katzcreates/BMOctoprint/Print Files/BMOctoprint_DisplayMount02.stl

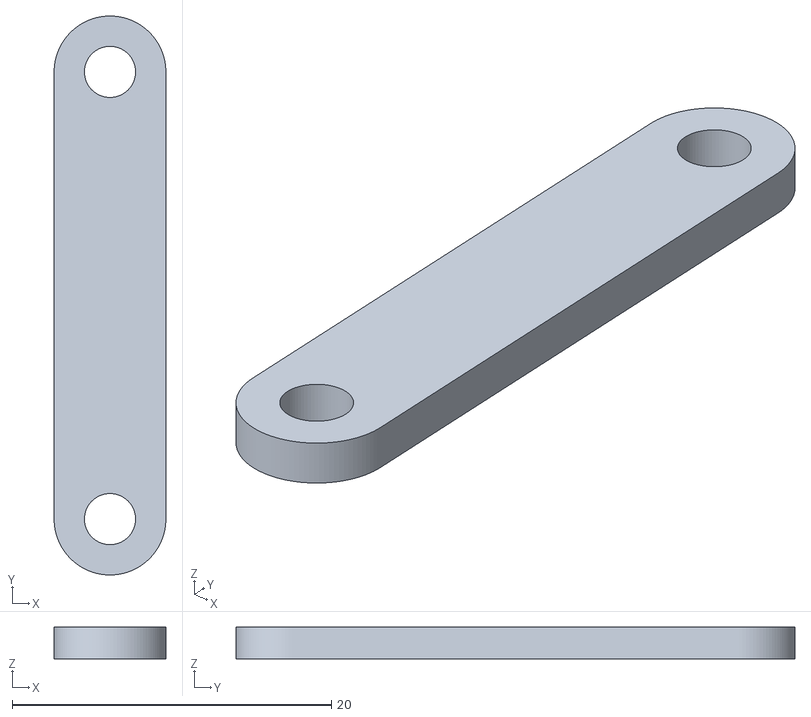
[picture p16: CAD file, 2022-08-17]
Print Files/BMOctoprint_DisplayMount02.stl
7.00 x 35.0 x 2.00
