katzcreates/BMOctoprint/Print Files/BMOctoprint_LegPlug.stl

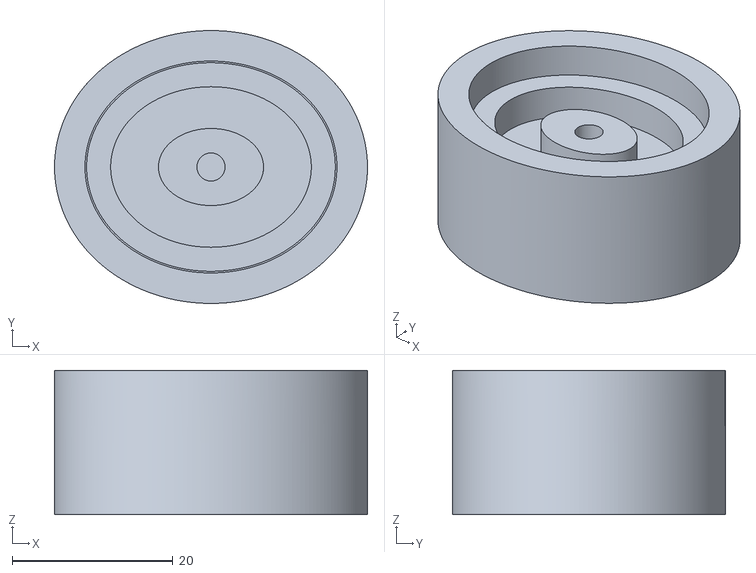
[picture p17: CAD file, 2022-08-17]
Print Files/BMOctoprint_LegPlug.stl
39.0 x 34.0 x 18.0
