katzcreates/BMOctoprint/Print Files/BMOctoprint_FacePlate.stl

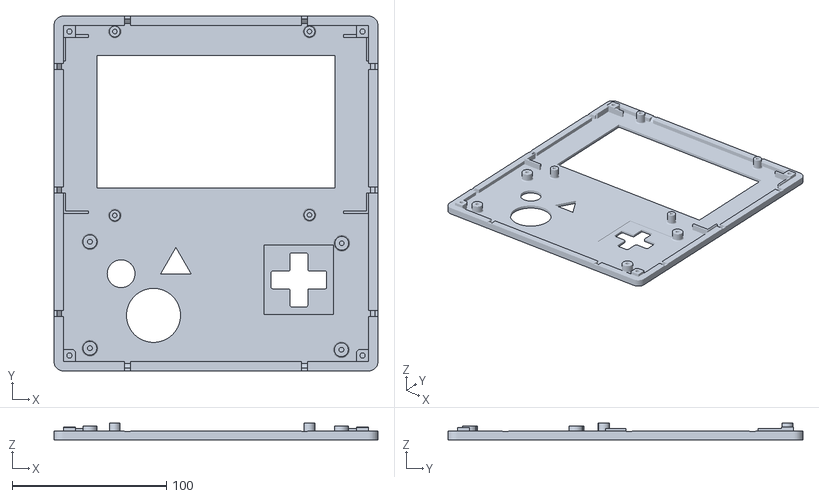
[picture p18: CAD file, 2022-08-17]
Print Files/BMOctoprint_FacePlate.stl
210.0 x 230.0 x 10.9
