katzcreates/BMOctoprint/Print Files/BMOctoprint_LeftPlate.stl

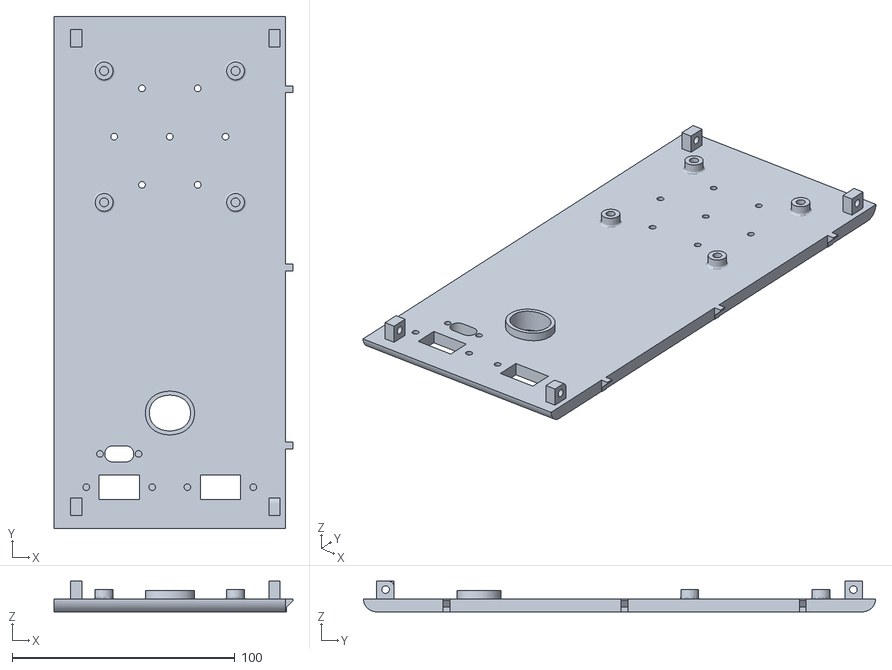
[picture p19: CAD file, 2022-08-17]
Print Files/BMOctoprint_LeftPlate.stl
107.3 x 230.0 x 13.8
