katzcreates/BMOctoprint/Print Files/BMOctoprint_DPad_CenterPin.stl

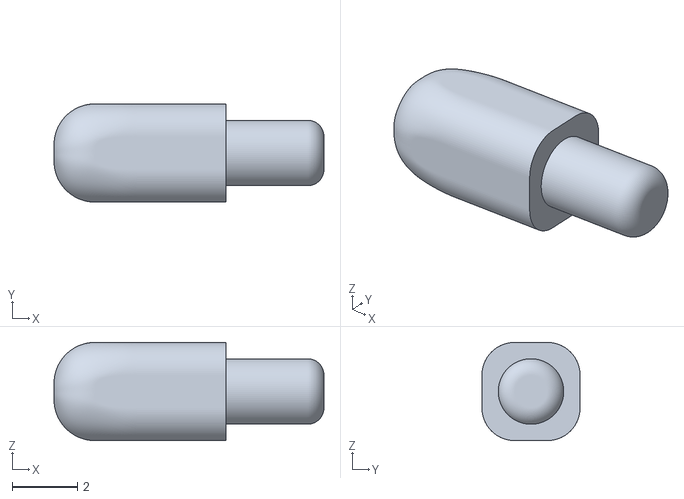
[picture p20: CAD file, 2022-08-17]
Print Files/BMOctoprint_DPad_CenterPin.stl
8.25 x 3.00 x 3.00
