katzcreates/BMOctoprint/Print Files/BMOctoprint_Arm_Segmented.stl

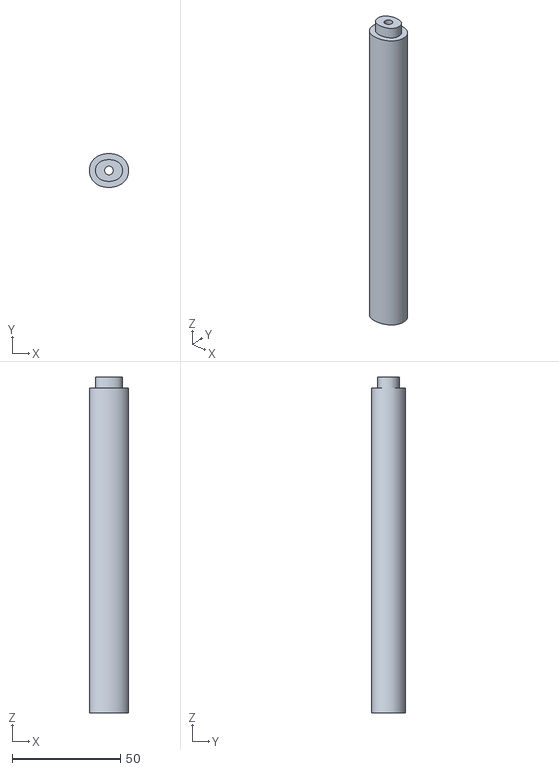
[picture p21: CAD file, 2022-08-17]
Print Files/BMOctoprint_Arm_Segmented.stl
18.0 x 15.6 x 155.0
