katzcreates/BMOctoprint/Print Files/BMOctoprint_Faceplate_RoundHoleCover.stl

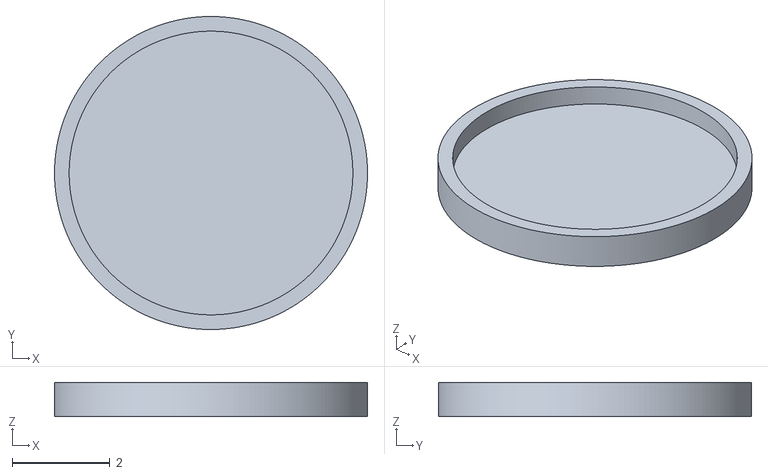
[picture p22: CAD file, 2022-08-17]
Print Files/BMOctoprint_Faceplate_RoundHoleCover.stl
6.40 x 6.40 x 0.7
