katzcreates/BMOctoprint/Print Files/BMOctoprint_LegJoint.stl

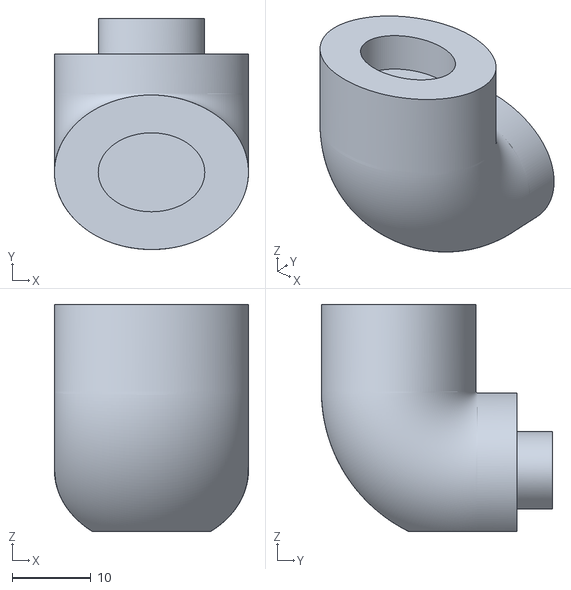
[picture p23: CAD file, 2022-08-17]
Print Files/BMOctoprint_LegJoint.stl
24.6 x 29.3 x 28.8
