katzcreates/BMOctoprint/Print Files/BMOctoprint_DPad_ButtonPushPad.stl

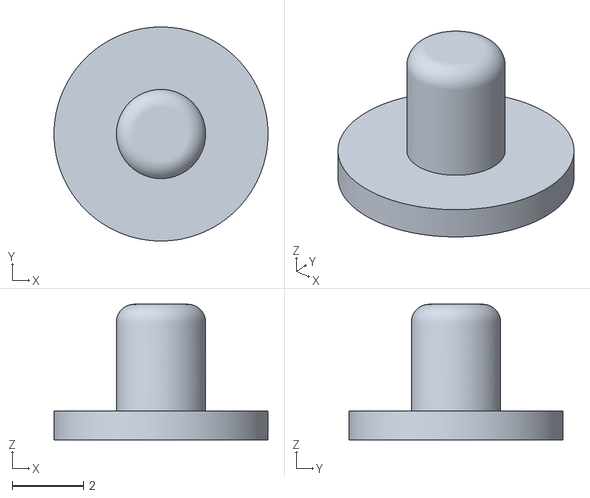
[picture p24: CAD file, 2022-08-17]
Print Files/BMOctoprint_DPad_ButtonPushPad.stl
6.00 x 6.00 x 3.80
