katzcreates/BMOctoprint/Print Files/BMOctoprint_DPad.stl

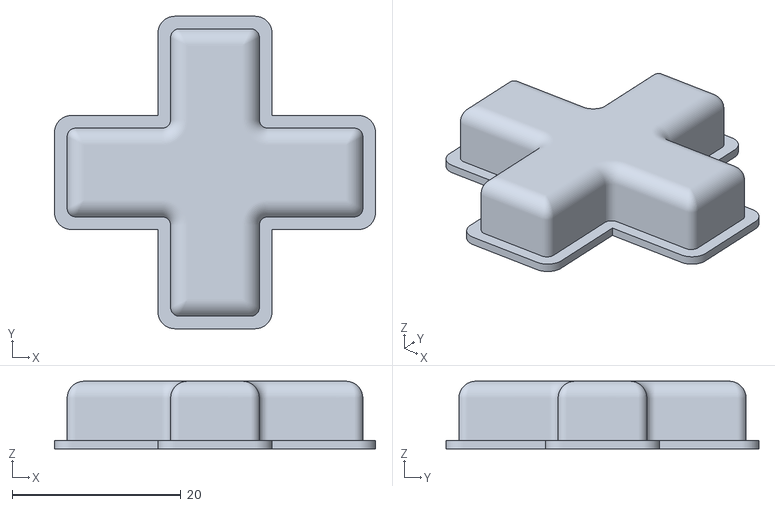
[picture p25: CAD file, 2022-08-17]
Print Files/BMOctoprint_DPad.stl
38.0 x 37.0 x 8.00
