katzcreates/BMOctoprint/Print Files/BMOctoprint_ArmPlug.stl

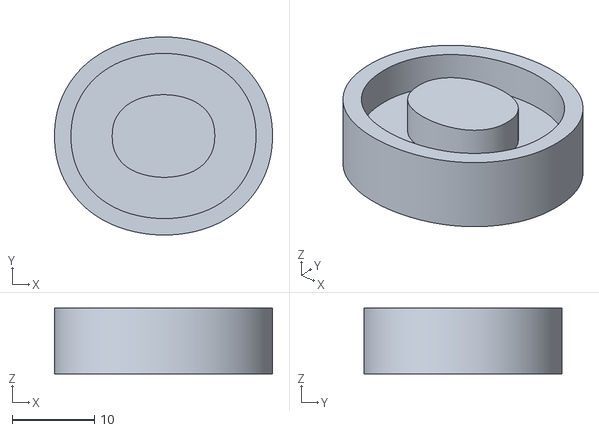
[picture p26: CAD file, 2022-08-17]
Print Files/BMOctoprint_ArmPlug.stl
26.4 x 24.0 x 8.00
