katzcreates/BMOctoprint/Print Files/BMOctoprint_LeftLeg.stl

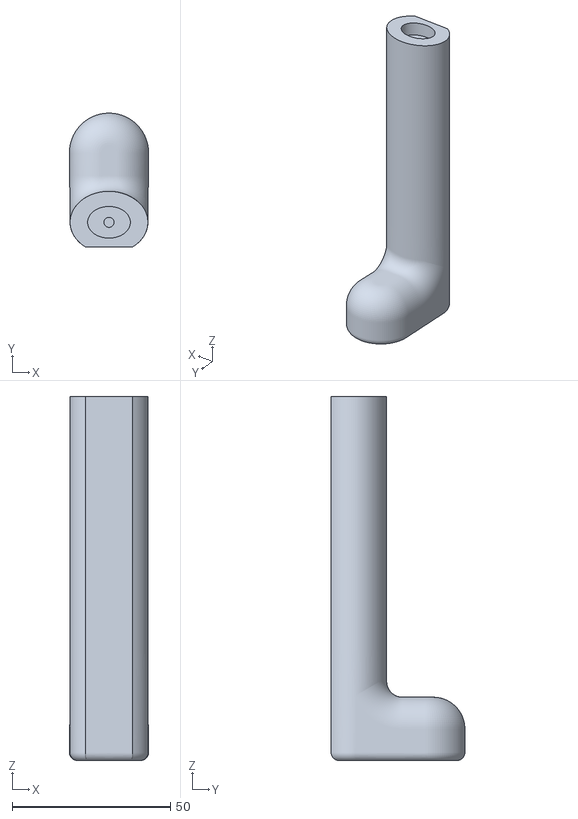
[picture p27: CAD file, 2022-08-17]
Print Files/BMOctoprint_LeftLeg.stl
25.0 x 42.3 x 115.0
