katzcreates/BMOctoprint/Print Files/BMOctoprint_Faceplate_MiddleHoleCover.stl

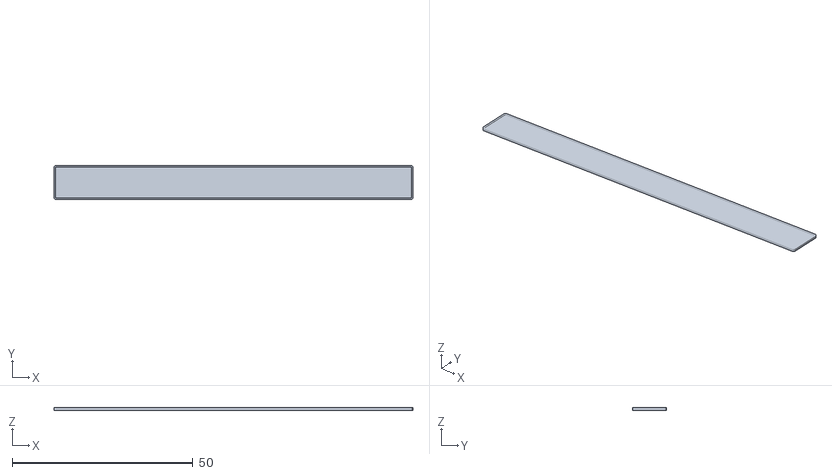
[picture p28: CAD file, 2022-08-17]
Print Files/BMOctoprint_Faceplate_MiddleHoleCover.stl
99.4 x 9.40 x 0.7
