katzcreates/BMOctoprint/Print Files/BMOctoprint_Faceplate_SmallHoleCover.stl

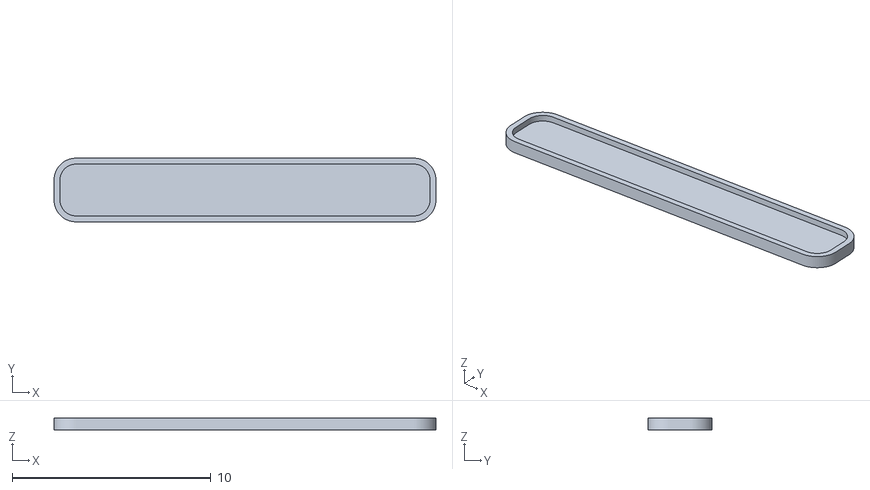
[picture p29: CAD file, 2022-08-17]
Print Files/BMOctoprint_Faceplate_SmallHoleCover.stl
19.2 x 3.20 x 0.6
