katzcreates/BMOctoprint/Print Files/BMOctoprint_Hand_Segmented.stl

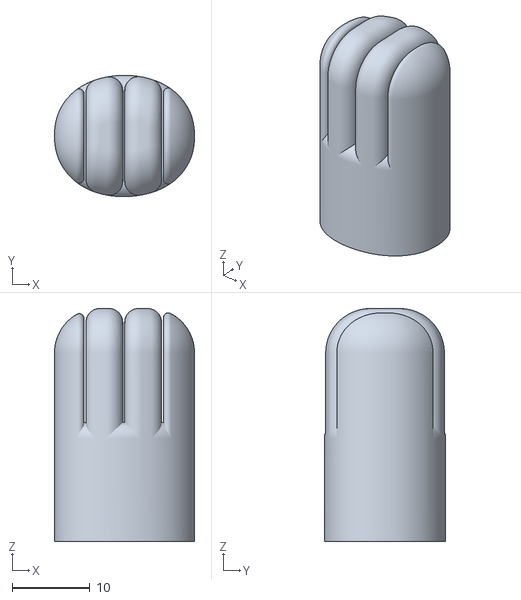
[picture p30: CAD file, 2022-08-17]
Print Files/BMOctoprint_Hand_Segmented.stl
18.0 x 15.6 x 30.0
