katzcreates/BMOctoprint/Print Files/BMOctoprint_TopPlate.stl

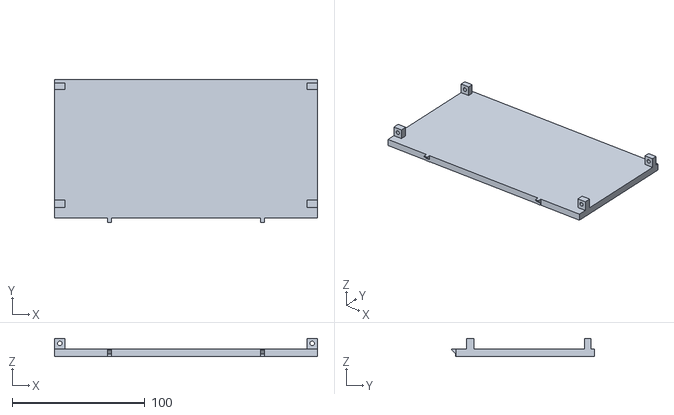
[picture p31: CAD file, 2022-08-17]
Print Files/BMOctoprint_TopPlate.stl
198.0 x 107.3 x 13.8
